samuelclay/pulse-bloom/blog/15121274332_e853484313_o.jpg

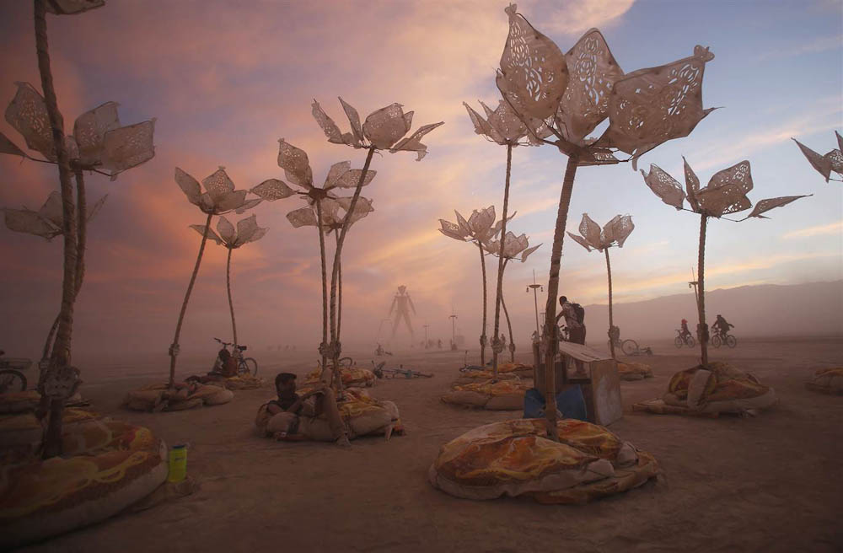
blog/15121274332_e853484313_o.jpg
