samuelclay/pulse-bloom/blog/Pulse & Bloom - First prototype.jpg

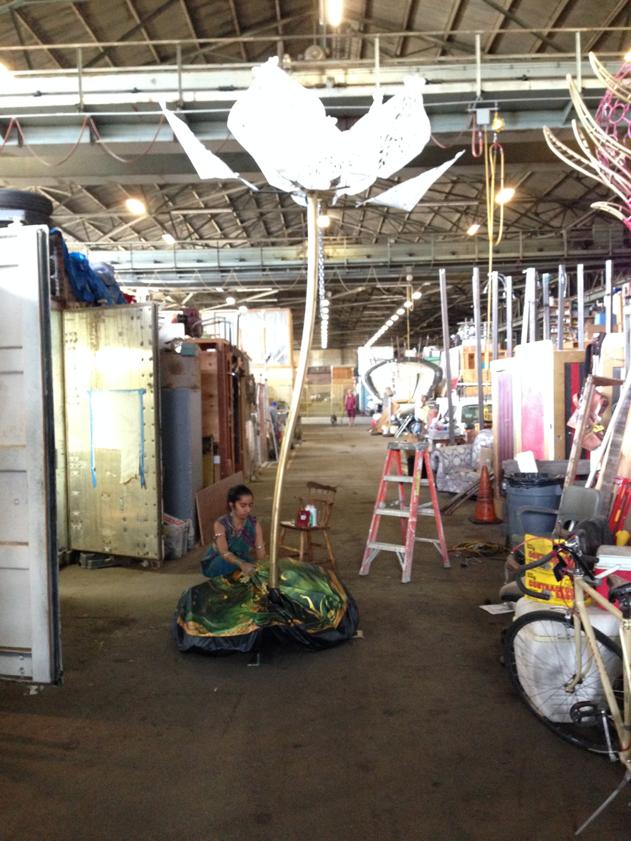
blog/Pulse & Bloom - First prototype.jpg
