samuelclay/pulse-bloom/blog/Pulse & Bloom - LEDs.jpg

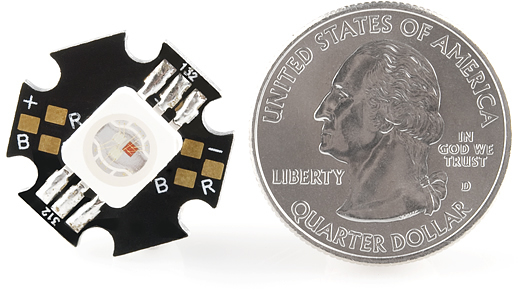
blog/Pulse & Bloom - LEDs.jpg
