samuelclay/pulse-bloom/blog/Pulse & Bloom - Naked Board.jpg

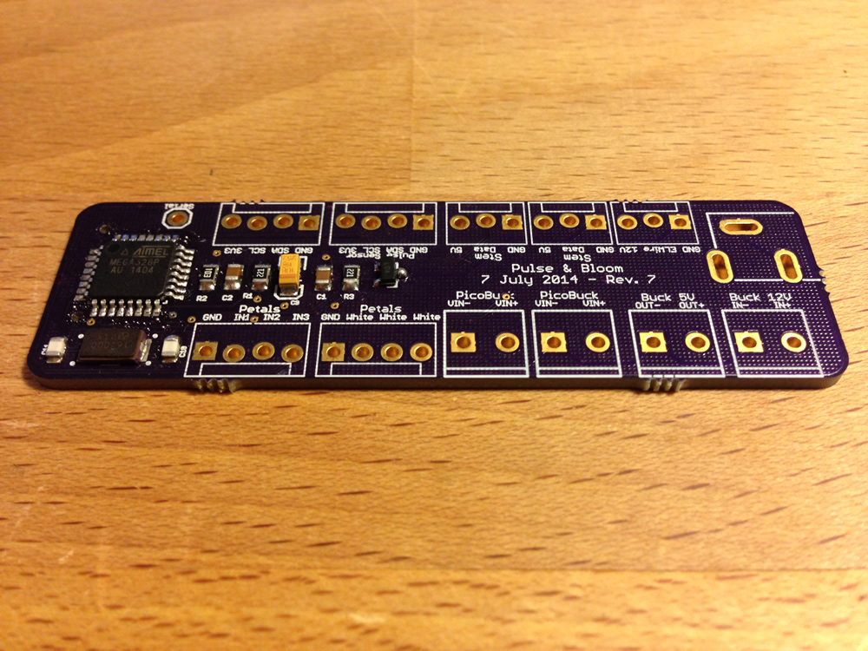
blog/Pulse & Bloom - Naked Board.jpg
