samuelclay/pulse-bloom/blog/Pulse & Bloom - Night.jpg

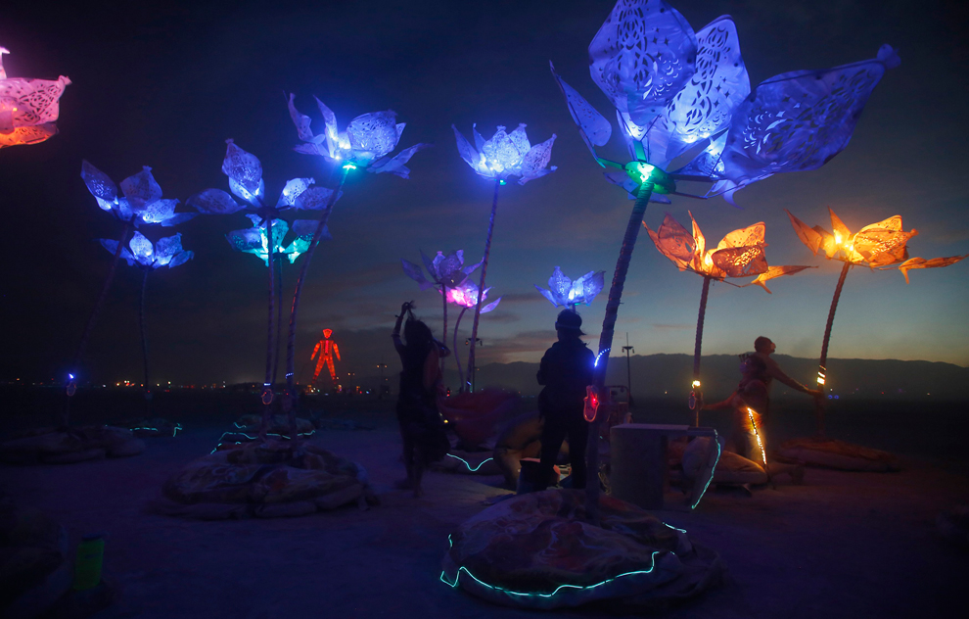
blog/Pulse & Bloom - Night.jpg
