samuelclay/pulse-bloom/blog/Pulse & Bloom - PicoBuck.jpg

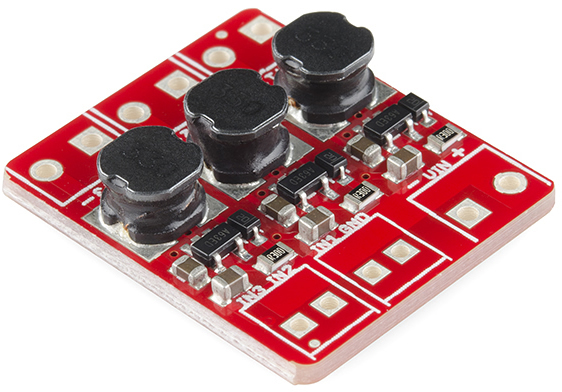
blog/Pulse & Bloom - PicoBuck.jpg
