samuelclay/pulse-bloom/blog/Pulse & Bloom - Raw Stems.jpg

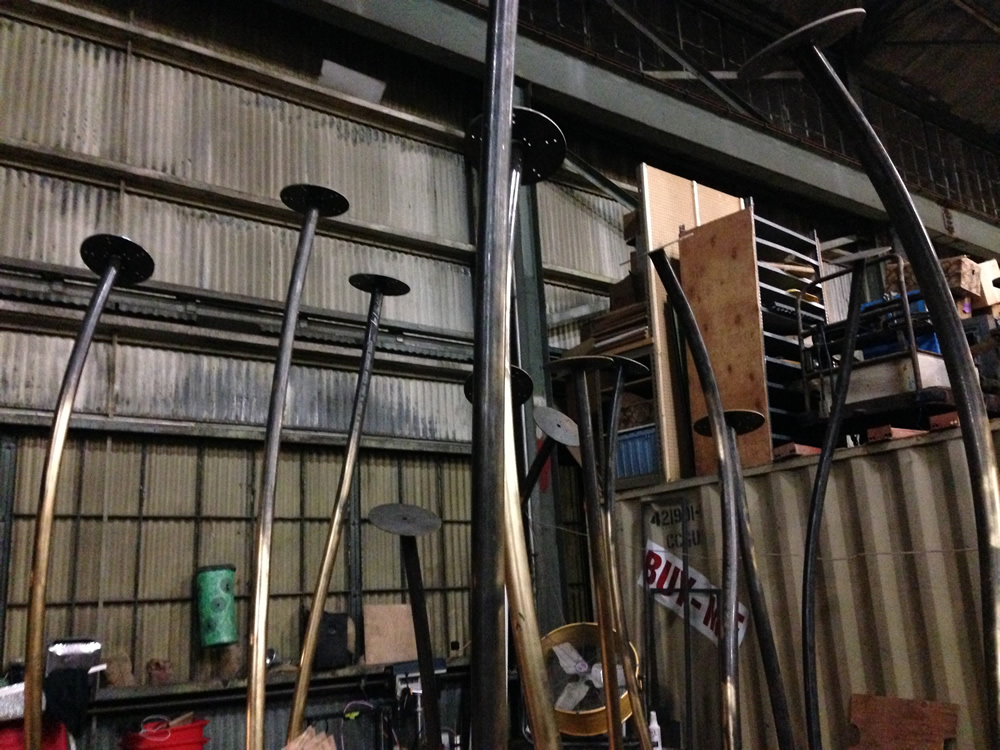
blog/Pulse & Bloom - Raw Stems.jpg
