samuelclay/pulse-bloom/blog/Pulse & Bloom - Reflowing boards.jpg

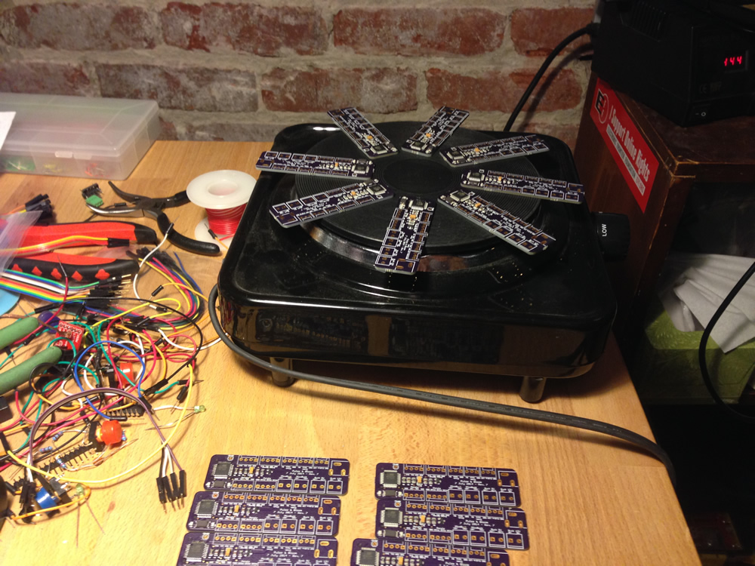
blog/Pulse & Bloom - Reflowing boards.jpg
