samuelclay/pulse-bloom/blog/Pulse & Bloom - Reflowing sensors.jpg

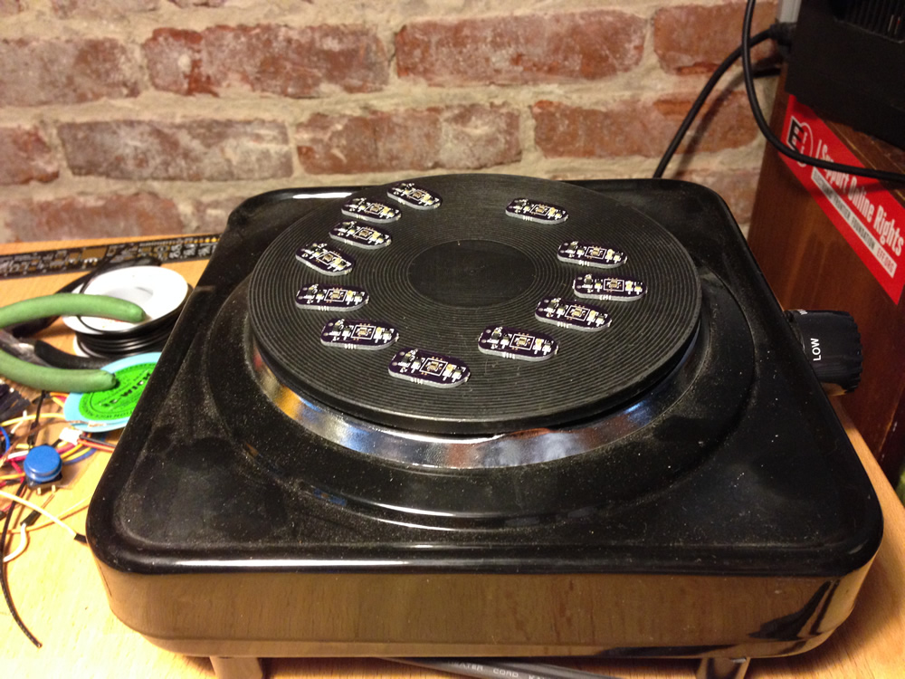
blog/Pulse & Bloom - Reflowing sensors.jpg
