samuelclay/pulse-bloom/blog/Pulse & Bloom - Sensor.jpg

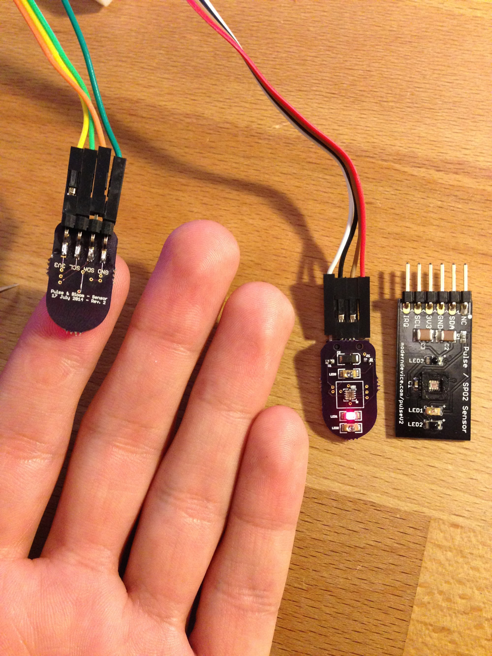
blog/Pulse & Bloom - Sensor.jpg
