samuelclay/pulse-bloom/blog/Pulse & Bloom - Van.jpg

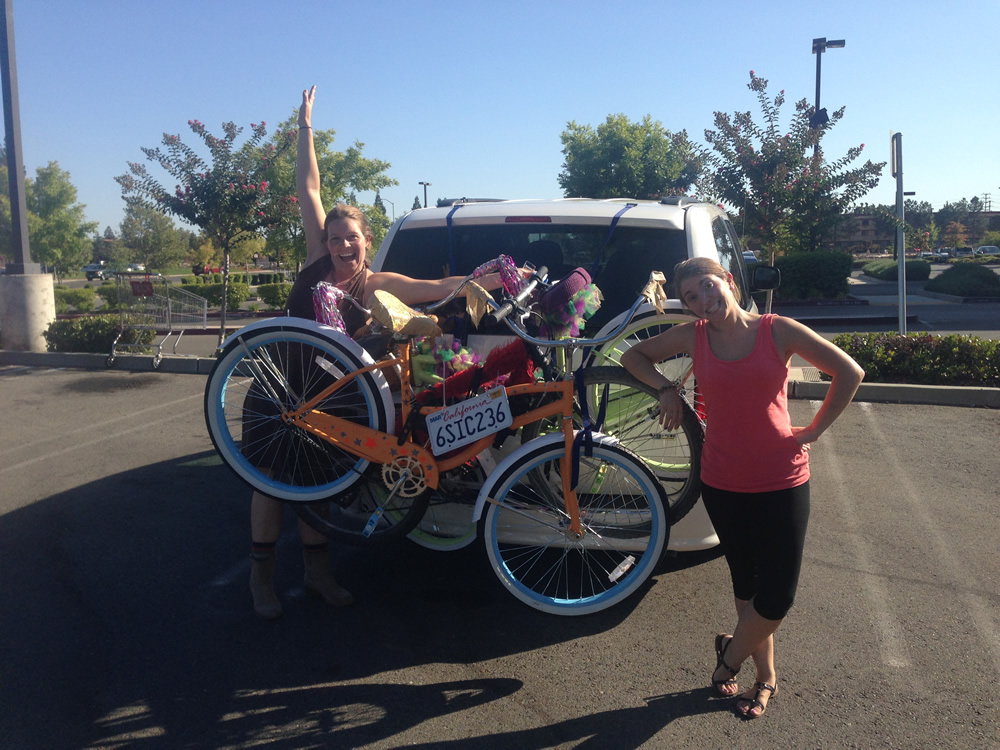
blog/Pulse & Bloom - Van.jpg
