samuelclay/pulse-bloom/src/smooth.cpp

#include "smooth.h"

float smooth(float data, float filterVal, float smoothedVal){

    if (filterVal > 1){      // check to make sure param's are within range
        filterVal = .99;
    }
    else if (filterVal <= 0.0){
        filterVal = 0.01;
    }

    smoothedVal = (data * (1.0 - filterVal)) + (smoothedVal  *  filterVal);
    return smoothedVal;
}
